seanstar12/dance-pad/ps_screenshot.PNG

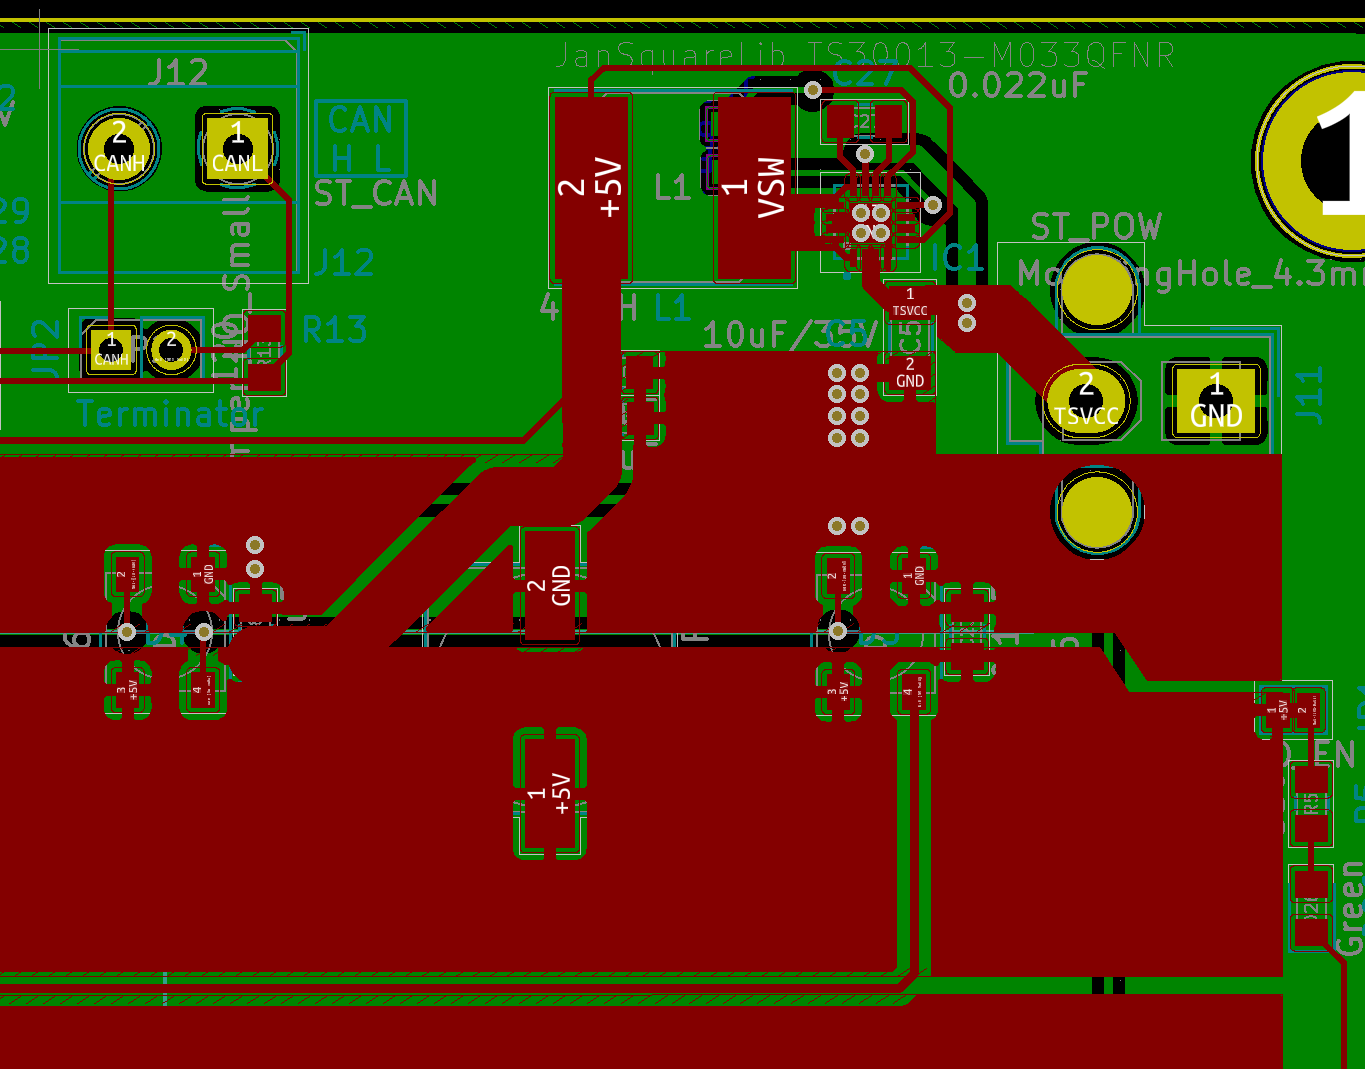
ps_screenshot.PNG
